djnugent/SolarNightLight/pics/IMG_20161212_190631548.jpg

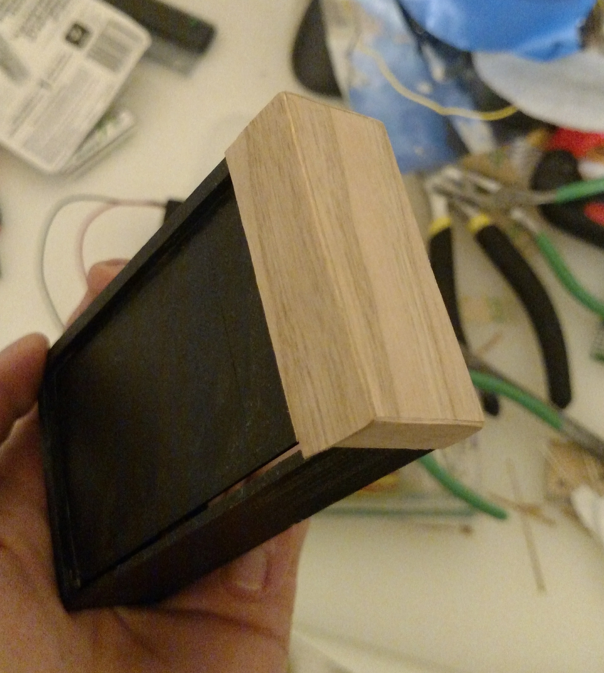
pics/IMG_20161212_190631548.jpg
