djnugent/SolarNightLight/pics/IMG_20161212_190706663.jpg

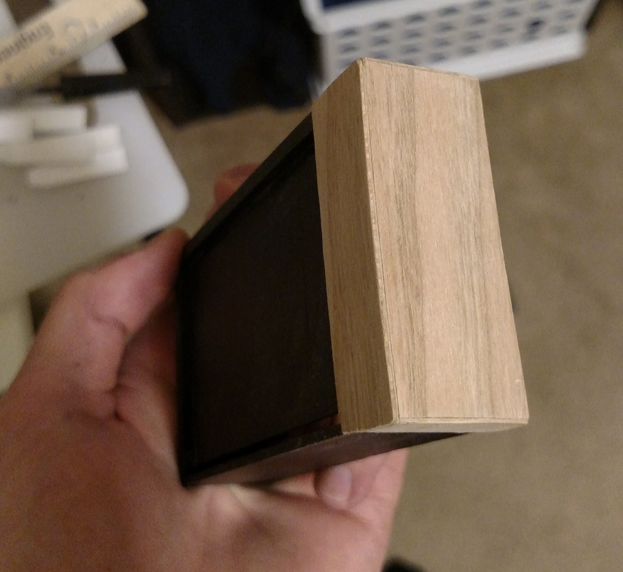
pics/IMG_20161212_190706663.jpg
