djnugent/SolarNightLight/pics/IMG_20161212_190723099.jpg

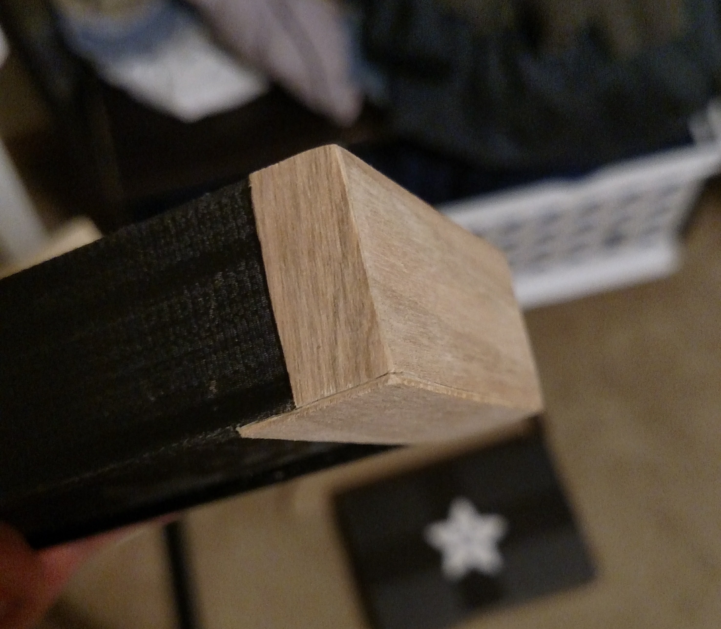
pics/IMG_20161212_190723099.jpg
