djnugent/SolarNightLight/pics/IMG_20161212_191030326.jpg

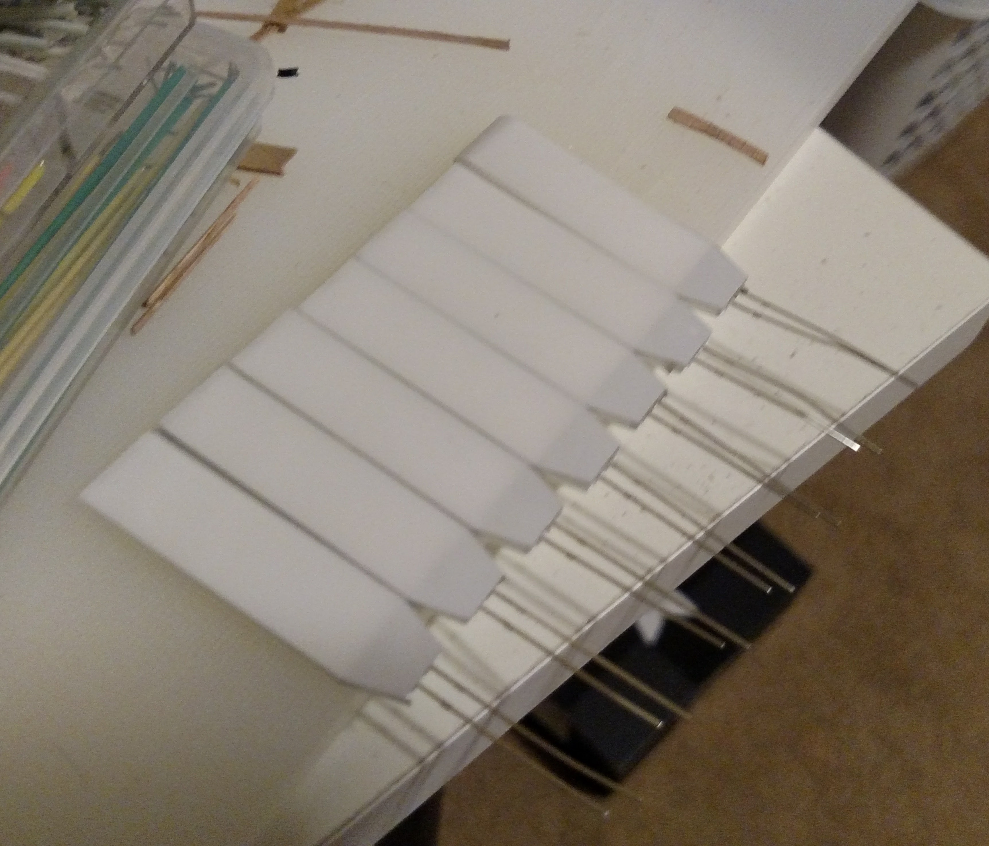
pics/IMG_20161212_191030326.jpg
