djnugent/SolarNightLight/pics/IMG_20161212_191118166.jpg

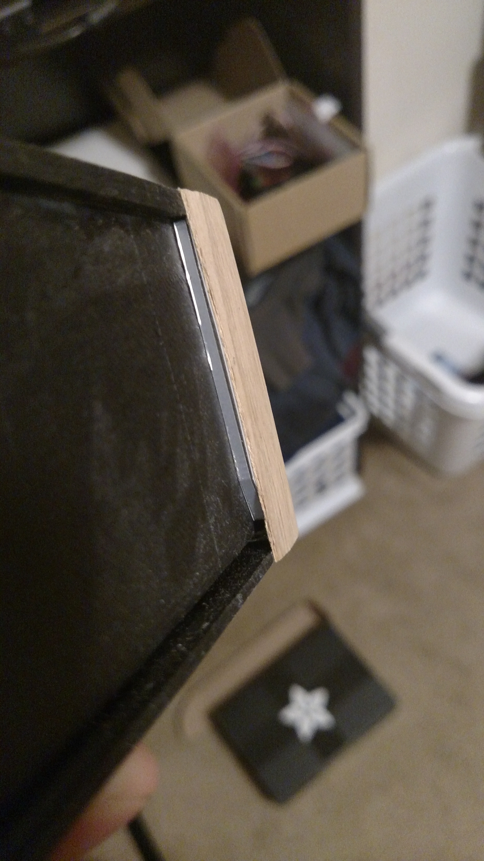
pics/IMG_20161212_191118166.jpg
