djnugent/SolarNightLight/pics/IMG_20161215_181129920.jpg

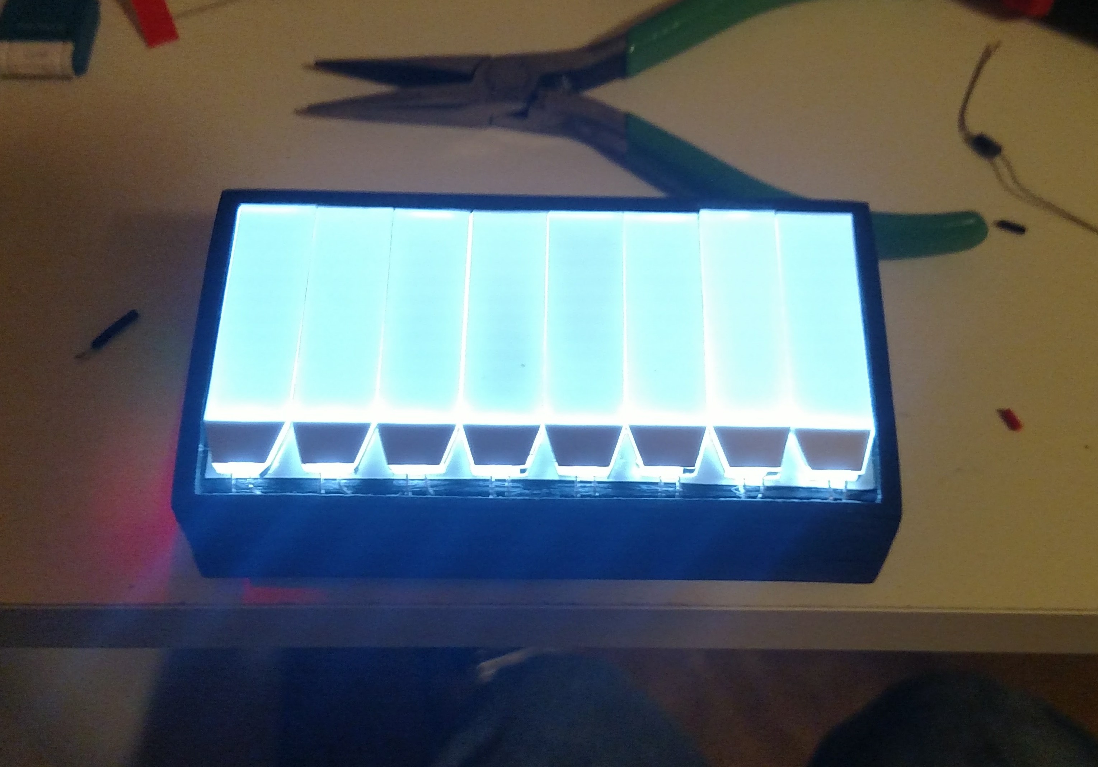
pics/IMG_20161215_181129920.jpg
