djnugent/SolarNightLight/pics/IMG_20161215_181137153.jpg

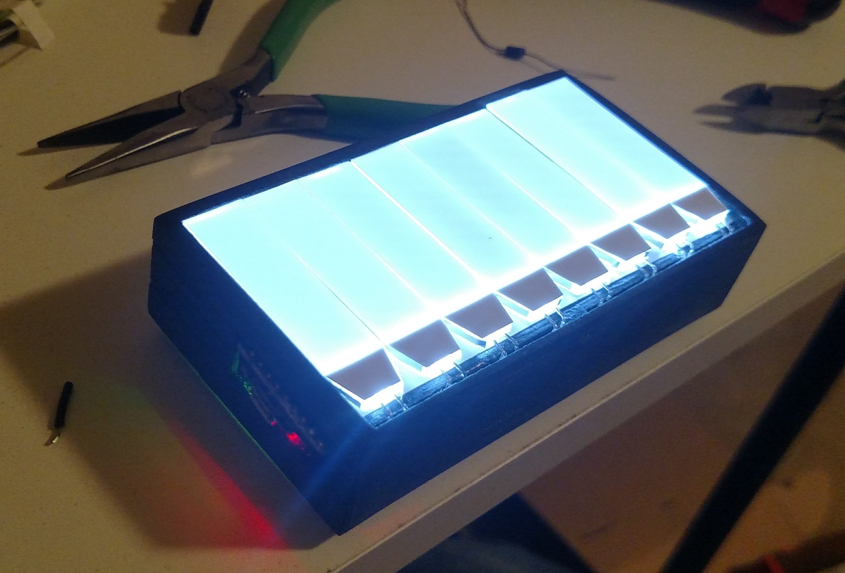
pics/IMG_20161215_181137153.jpg
