djnugent/SolarNightLight/pics/IMG_20161215_190656090.jpg

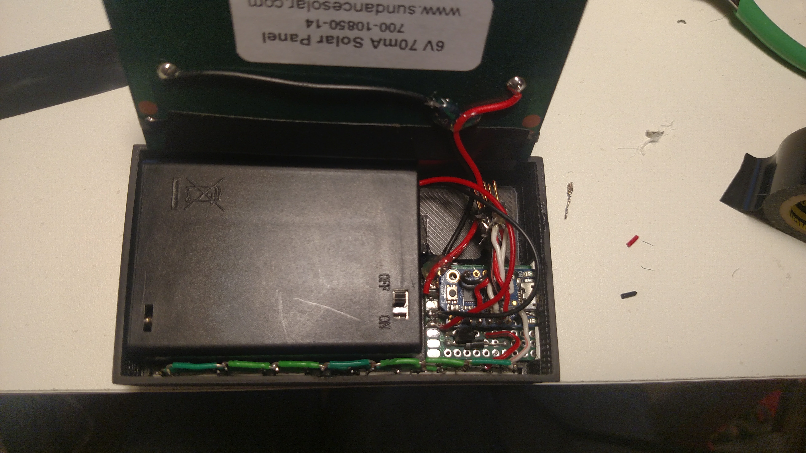
pics/IMG_20161215_190656090.jpg
