djnugent/SolarNightLight/pics/IMG_20161215_194118334.jpg

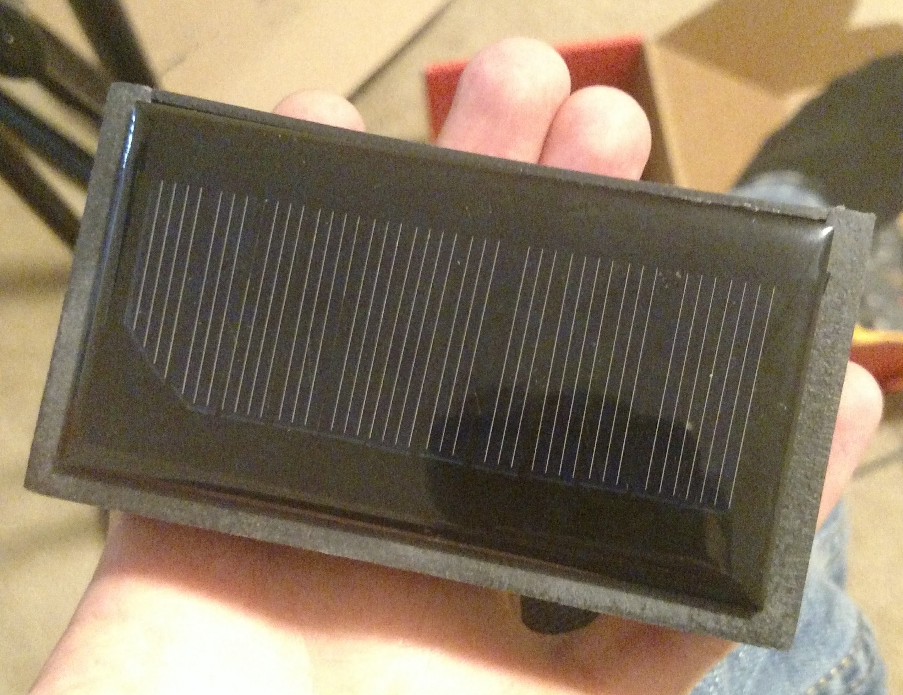
pics/IMG_20161215_194118334.jpg
