djnugent/SolarNightLight/pics/IMG_20161215_194144050.jpg

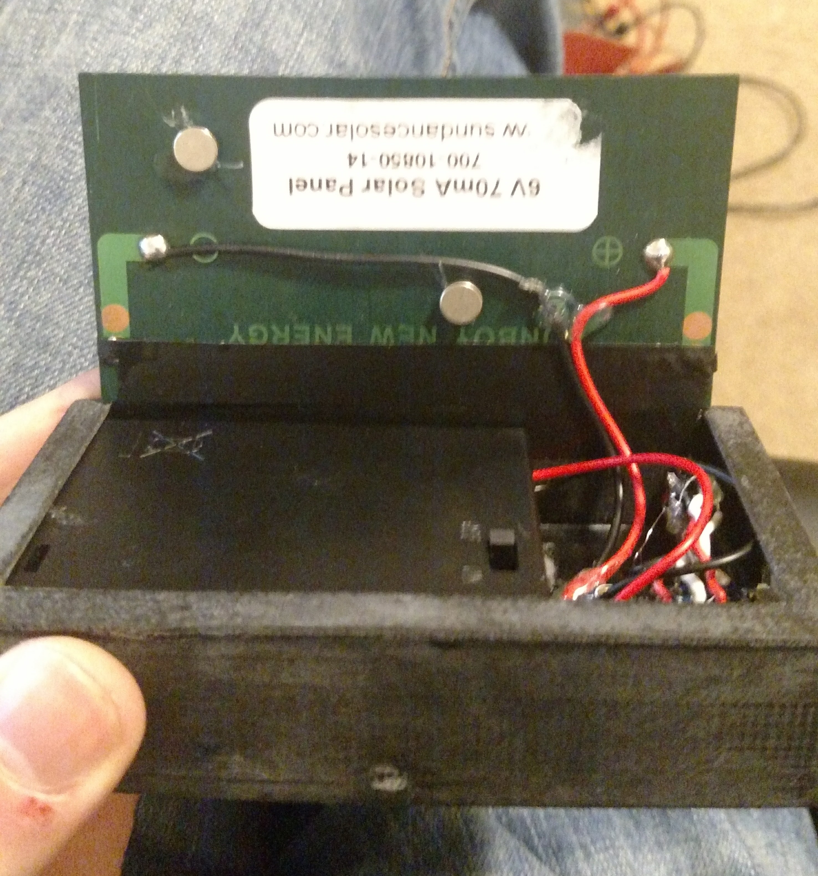
pics/IMG_20161215_194144050.jpg
