djnugent/SolarNightLight/pics/IMG_20161215_202210214.jpg

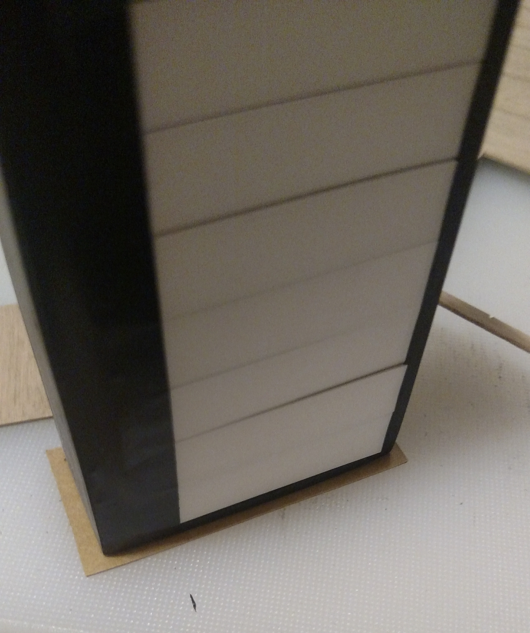
pics/IMG_20161215_202210214.jpg
