djnugent/SolarNightLight/pics/IMG_20161215_214545791.jpg

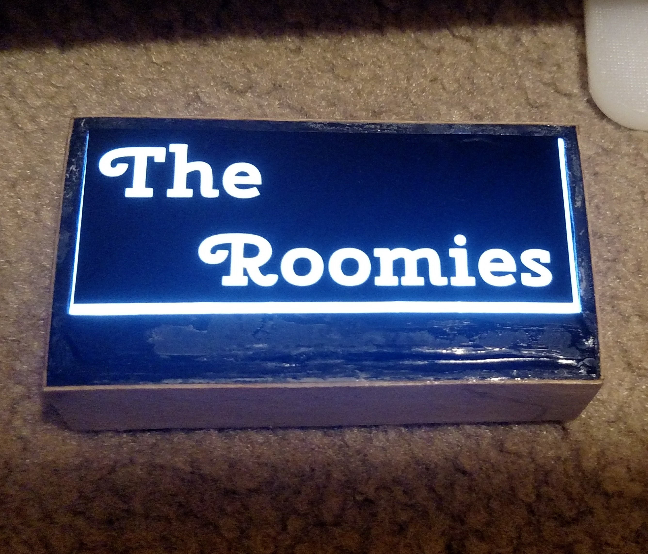
pics/IMG_20161215_214545791.jpg
