djnugent/SolarNightLight/pics/IMG_20161215_220026863.jpg

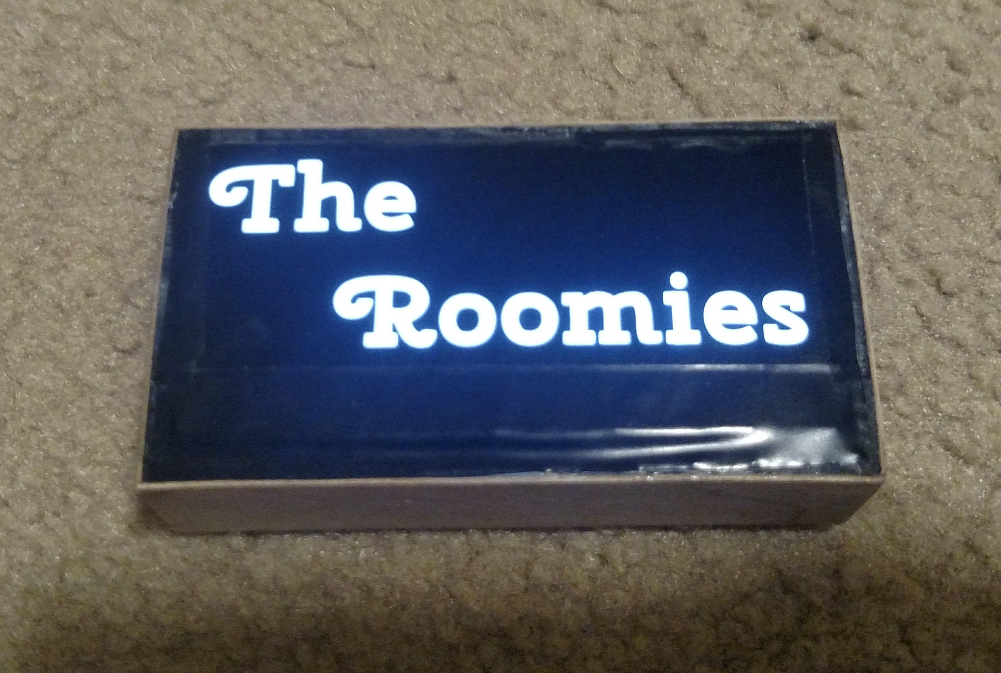
pics/IMG_20161215_220026863.jpg
