djnugent/SolarNightLight/pics/IMG_20170104_130709996.jpg

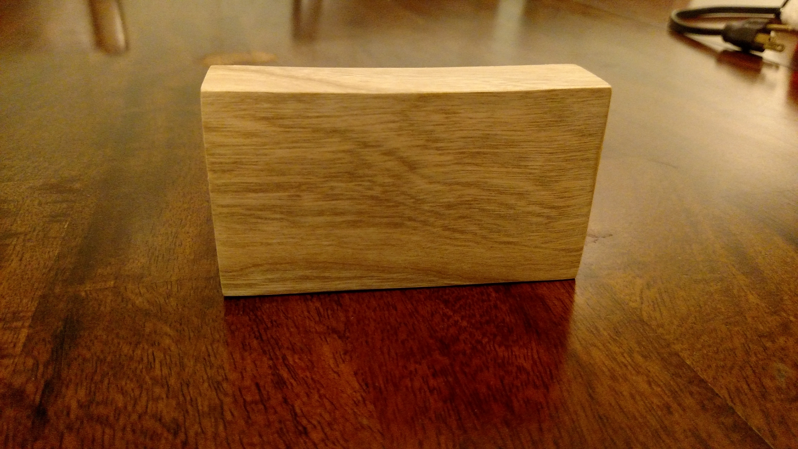
pics/IMG_20170104_130709996.jpg
