djnugent/SolarNightLight/pics/IMG_20170104_130716102.jpg

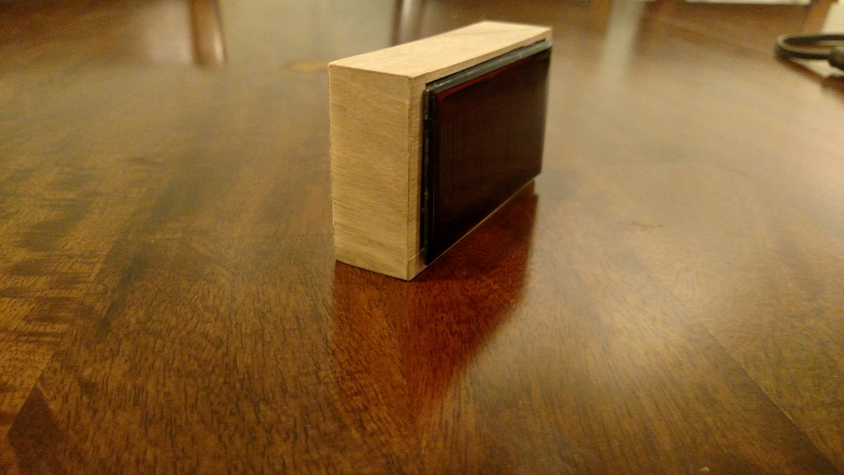
pics/IMG_20170104_130716102.jpg
