djnugent/SolarNightLight/pics/IMG_20170104_130725834.jpg

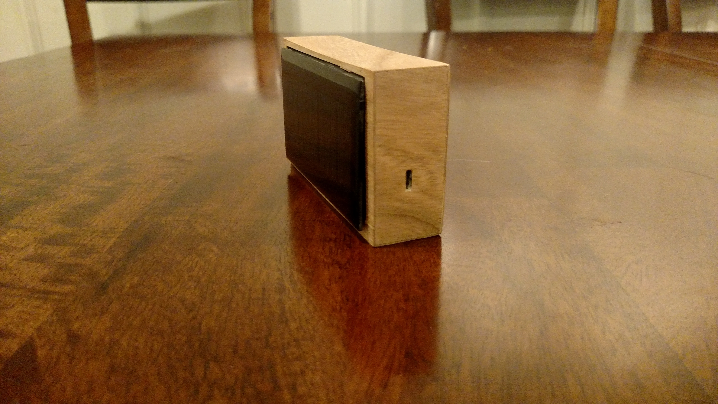
pics/IMG_20170104_130725834.jpg
