djnugent/SolarNightLight/pics/IMG_20170108_210904779.jpg

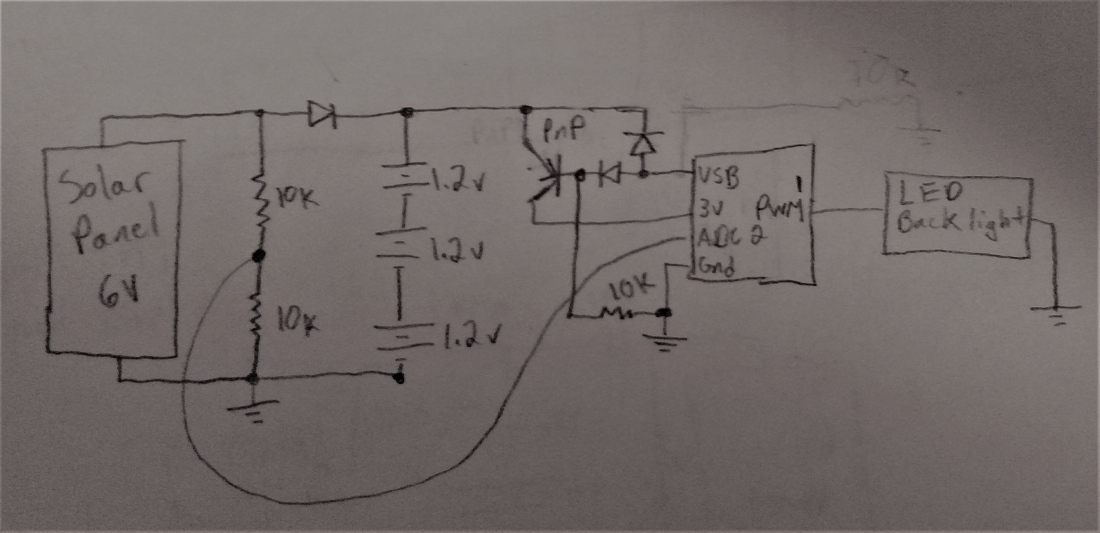
pics/IMG_20170108_210904779.jpg
