djnugent/SolarNightLight/pics/IMG_20170108_210930519.jpg

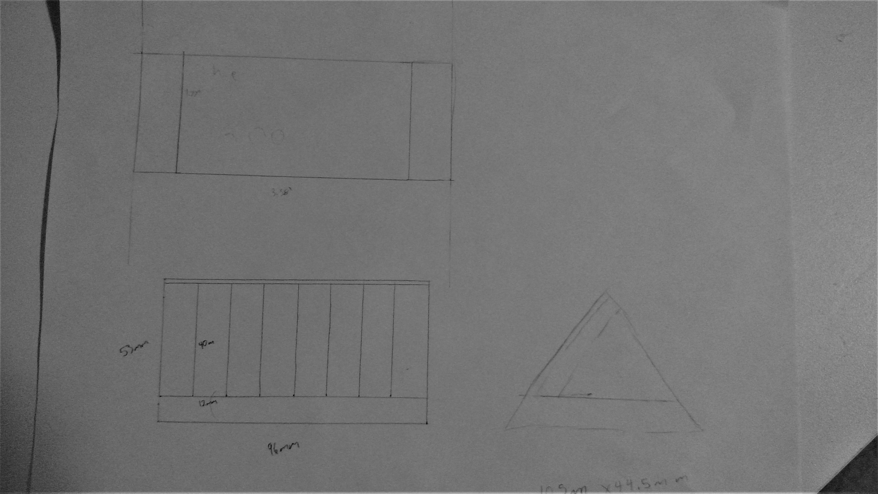
pics/IMG_20170108_210930519.jpg
